AlbertPhan/stat-tracker/include/usb-cdc.c

/**
 * USB CDC Implementation
 * Based on the example from
 * https://github.com/Blinkinlabs/ch554_sdcc/tree/master/examples/usb_device_cdc_i2c
 *
 * Andreas Butti, (c) 2019
 * License: GPL
 */

#include "inc.h"
#include "usb-cdc.h"
#include "hardware.h"
//#include "logic.h"
#include "usb-descriptor.h"
//#include "parser.h"
//#include "eeprom.h"


/**
 * Last setup request
 */
__xdata uint8_t g_SetupReq;

/**
 * USB Configuration, can be read and written by the host
 */
__xdata uint8_t g_UsbConfig;

/**
 * Pointer to the current configuration data,
 * this pointer is incremented on transmission,
 * if a block is sent, while g_SetupLen is decremented
 */
const uint8_t* g_pDescr;

/**
 * Setup length, is decremented if a block is sent, see g_pDescr
 */
__xdata uint16_t g_SetupLen;

// Buffer for dynamic generated setup responses
__xdata uint8_t g_SetupRamBuffer[34];

/**
 * Use the received data as Setup request
 */
#define UsbSetupBuf	((PUSB_SETUP_REQ)Ep0Buffer)

// Configures DTE rate, stop-bits, parity, and number-of-character
#define SET_LINE_CODING 0X20

// This request allows the host to find out the currently configured line coding.
#define GET_LINE_CODING 0X21

// This request generates RS-232/V.24 style control signals
#define SET_CONTROL_LINE_STATE 0X22

/**
 * Baud rate, not needed for Virtual USB without hardware Serial
 * But may this is needed for another project, therefore this
 * will not be removed
 */
uint32_t g_Baud = 0;

// CDC parameter
// The initial baud rate is 57600, 1 stop bit, no parity, 8 data bits.
__xdata uint8_t g_LineCoding[7] = { 0x00, 0xe1, 0x00, 0x00, 0x00, 0x00, 0x08 };

// Serial receive buffer size
#define UART_REV_LEN 64

// Serial receive buffer
__idata uint8_t g_Receive_Uart_Buf[UART_REV_LEN];

// The circular buffer write pointer, the bus reset needs to be initialized to 0
volatile __idata uint8_t g_Uart_Input_Point = 0;

// The circular buffer fetches the pointer, and the bus reset needs to be initialized to 0.
volatile __idata uint8_t g_Uart_Output_Point = 0;

// Current buffer remaining bytes to be fetched
volatile __idata uint8_t g_UartByteCount = 0;

// Data received on behalf of the USB endpoint
volatile __idata uint8_t g_USBByteCount = 0;

// Data pointer
volatile __idata uint8_t g_USBBufOutPoint = 0;

// Upload endpoint is busy flag
volatile __idata uint8_t g_UpPoint2_Busy = 0;

/**
 * Handle USB Reset
 */
inline void usbResetInterrupt() {
	UEP0_CTRL = UEP_R_RES_ACK | UEP_T_RES_NAK;
	UEP1_CTRL = bUEP_AUTO_TOG | UEP_T_RES_NAK;
	UEP2_CTRL = bUEP_AUTO_TOG | UEP_T_RES_NAK | UEP_R_RES_ACK;
	USB_DEV_AD = 0x00;
	UIF_SUSPEND = 0;
	UIF_TRANSFER = 0;

	// Clear interrupt flag
	UIF_BUS_RST = 0;

	// Circular buffer input pointer
	g_Uart_Input_Point = 0;

	// Circular buffer read pointer
	g_Uart_Output_Point = 0;

	// Current buffer remaining bytes to be fetched
	g_UartByteCount = 0;

	// Length received by the USB endpoint
	g_USBByteCount = 0;

	// Clear configuration value
	g_UsbConfig = 0;
	g_UpPoint2_Busy = 0;
}

/**
 * Handle USB Suspend
 */
inline void usbWakeupSuspendInterrupt() {
	if (USB_MIS_ST & bUMS_SUSPEND) {
		while (XBUS_AUX & bUART0_TX) {
			; // Waiting for transmission to complete
		}

		// Before turning of the CPU turn OFF the LEDs
		//turnOffLeds();

		SAFE_MOD = 0x55;
		SAFE_MOD = 0xAA;

		// USB or RXD0/1 can be woken up when there is a signal
		WAKE_CTRL = bWAK_BY_USB | bWAK_RXD0_LO | bWAK_RXD1_LO;

		// Sleep
		PCON |= PD;

		SAFE_MOD = 0x55;
		SAFE_MOD = 0xAA;
		WAKE_CTRL = 0x00;
	}
}


/**
 * Transmit a Setup Block, increment pointer,
 * decrement remaining block length.
 * Calculate Length
 *
 * @param len Length
 * @return Length
 */
uint8_t transmitSetupBlock(uint8_t len) {
	// This transmission length
	len = g_SetupLen >= DEFAULT_ENDP0_SIZE ? DEFAULT_ENDP0_SIZE : g_SetupLen;

	// Load upload data, increment pointer, so the data is transmitted in Blocks
	memcpy(Ep0Buffer, g_pDescr, len);
	g_SetupLen -= len;
	g_pDescr += len;

	return len;
}


/**
 * Check if there is a custom PID / VID Configured, and overwrite the basic one
 * This is used to force e.g. Windows 7 to use a specific driver
 
void prepareUsbIds() {
	uint8_t a = 0;

	if (ReadDataFlash(4, 1, &a) != 1) {
		return;
	}

	// Use this char at pos 5 on EEPROM to mark the PID / VID should be loaded
	if (a != '>') {
		return;
	}

	if (ReadDataFlash(0, 1, &a) != 1) {
		return;
	}
	g_SetupRamBuffer[9] = a;

	if (ReadDataFlash(1, 1, &a) != 1) {
		return;
	}
	g_SetupRamBuffer[8] = a;

	if (ReadDataFlash(2, 1, &a) != 1) {
		return;
	}
	g_SetupRamBuffer[11] = a;

	if (ReadDataFlash(3, 1, &a) != 1) {
		return;
	}
	g_SetupRamBuffer[10] = a;
}
*/

/**
 * Read custom serial from EEPROM
 *
 * @return Len, 0x00 if nothing was read
 
inline uint8_t readNameFromEeprom() {
	uint8_t i;

	if (ReadDataFlash(24, sizeof(g_SetupRamBuffer) - 2, g_SetupRamBuffer + 2) != 1) {

		for (i = 2; i < sizeof(g_SetupRamBuffer) - 1; i += 2) {

			if (g_SetupRamBuffer[i] == 255 || (g_SetupRamBuffer[i] == 0 && g_SetupRamBuffer[i + 1] == 0)) {
				if (i > 2) {
					return i;
				} else {
					break;
				}
			}
		}
	}

	return 0x00;
}
*/

/**
 * Process USB Standard setup request
 *
 * @return Length
 */
inline uint8_t processUsbDescriptionRequest() {
	uint8_t len = 0;

	switch (UsbSetupBuf->wValueH) {
	// Device descriptor
	case 1:
		// Send the device descriptor to the buffer to be sent
		len = sizeof(g_DescriptorDevice);
		memcpy(g_SetupRamBuffer, g_DescriptorDevice, len);

		// Update USB IDs 
		//prepareUsbIds();
		// commented out to disable EEPROM ID functionality

		g_pDescr = g_SetupRamBuffer;
		break;

	// Configuration descriptor
	case 2:
		// Send the device descriptor to the buffer to be sent
		g_pDescr = g_DescriptorConfiguration;
		len = sizeof(g_DescriptorConfiguration);
		break;

	case 3:
		if (UsbSetupBuf->wValueL == 0) {
			g_pDescr = g_DescriptorLanguage;
			len = sizeof(g_DescriptorLanguage);

		} else if (UsbSetupBuf->wValueL == 1) {
			g_pDescr = g_DescriptorManufacturer;
			len = sizeof(g_DescriptorManufacturer);

		} else if (UsbSetupBuf->wValueL == 2) {
			/*
			len = readNameFromEeprom();
			if (len == 0x00) {
				g_pDescr = g_DescriptorProduct;
				len = sizeof(g_DescriptorProduct);
			} else {
				g_pDescr = g_SetupRamBuffer;
				g_SetupRamBuffer[0] = len;
				g_SetupRamBuffer[1] = 3;
			}
			*/
			g_pDescr = g_DescriptorProduct;
			len = sizeof(g_DescriptorProduct);			
		} else {
			g_pDescr = g_DescriptorSerial;
			len = sizeof(g_DescriptorSerial);
		}
		break;

	default:
		// Unsupported command or error
		len = 0xff;
		break;
	}

	if (g_SetupLen > len) {
		// Limit total length
		g_SetupLen = len;
	}

	return transmitSetupBlock(len);
}

/**
 * Process USB Standard setup clear request
 *
 * @return Length
 */
inline uint8_t processStandardSetupClearRequest() {
	uint8_t len = 0;

	// Clear device
	if ((UsbSetupBuf->bRequestType & 0x1F) == USB_REQ_RECIP_DEVICE) {
		if ((((uint16_t) UsbSetupBuf->wValueH << 8) | UsbSetupBuf->wValueL) == 0x01) {
			if (g_DescriptorConfiguration[7] & 0x20) {
				// wake
			} else {
				// operation failed
				len = 0xff;
			}
		} else {
			// operation failed
			len = 0xff;
		}

	} else if ((UsbSetupBuf->bRequestType & USB_REQ_RECIP_MASK) == USB_REQ_RECIP_ENDP) {
		switch (UsbSetupBuf->wIndexL) {
		case 0x83:
			UEP3_CTRL = UEP3_CTRL & ~(bUEP_T_TOG | MASK_UEP_T_RES) | UEP_T_RES_NAK;
			break;

		case 0x03:
			UEP3_CTRL = UEP3_CTRL & ~(bUEP_R_TOG | MASK_UEP_R_RES) | UEP_R_RES_ACK;
			break;

		case 0x82:
			UEP2_CTRL = UEP2_CTRL & ~(bUEP_T_TOG | MASK_UEP_T_RES) | UEP_T_RES_NAK;
			break;

		case 0x02:
			UEP2_CTRL = UEP2_CTRL & ~(bUEP_R_TOG | MASK_UEP_R_RES) | UEP_R_RES_ACK;
			break;

		case 0x81:
			UEP1_CTRL = UEP1_CTRL & ~(bUEP_T_TOG | MASK_UEP_T_RES) | UEP_T_RES_NAK;
			break;

		case 0x01:
			UEP1_CTRL = UEP1_CTRL & ~(bUEP_R_TOG | MASK_UEP_R_RES) | UEP_R_RES_ACK;
			break;

		default:
			// Unsupported endpoint
			len = 0xff;
			break;
		}

	} else {
		// No endpoints are not supported
		len = 0xff;
	}
	return len;
}

/**
 * Process USB Standard setup set feature request
 *
 * @return Length
 */
inline uint8_t processStandardSetupSetFeatureRequest() {
	// defaults to operation failed
	uint8_t len = 0xff;

	// Setting up the device
	if ((UsbSetupBuf->bRequestType & 0x1F) == USB_REQ_RECIP_DEVICE) {
		if ((((uint16_t) UsbSetupBuf->wValueH << 8) | UsbSetupBuf->wValueL) == 0x01) {
			if (g_DescriptorConfiguration[7] & 0x20) {
				// Sleep
				while (XBUS_AUX & bUART0_TX) {
					;	// Waiting for transmission to complete
				}

				SAFE_MOD = 0x55;
				SAFE_MOD = 0xAA;

				// USB or RXD0 / 1 can be woken up when there is a signal
				WAKE_CTRL = bWAK_BY_USB | bWAK_RXD0_LO | bWAK_RXD1_LO;

				// Sleep
				PCON |= PD;

				SAFE_MOD = 0x55;
				SAFE_MOD = 0xAA;
				WAKE_CTRL = 0x00;

				// result success
				len = 0;
			}
		}

		// Set endpoint
	} else if ((UsbSetupBuf->bRequestType & 0x1F) == USB_REQ_RECIP_ENDP) {
		if ((((uint16_t) UsbSetupBuf->wValueH << 8) | UsbSetupBuf->wValueL) == 0x00) {
			// result success
			len = 0;

			switch (((uint16_t) UsbSetupBuf->wIndexH << 8) | UsbSetupBuf->wIndexL) {
			case 0x83:
				// Set endpoint 3 IN STALL
				UEP3_CTRL = UEP3_CTRL & (~bUEP_T_TOG) | UEP_T_RES_STALL;
				break;

			case 0x03:
				// Set Endpoint 3 OUT Stall
				UEP3_CTRL = UEP3_CTRL & (~bUEP_R_TOG) | UEP_R_RES_STALL;
				break;

			case 0x82:
				// Set endpoint 2 IN STALL
				UEP2_CTRL = UEP2_CTRL & (~bUEP_T_TOG) | UEP_T_RES_STALL;
				break;

			case 0x02:
				// Set Endpoint 2 OUT Stall
				UEP2_CTRL = UEP2_CTRL & (~bUEP_R_TOG) | UEP_R_RES_STALL;
				break;

			case 0x81:
				// Set endpoint 1 IN STALL
				UEP1_CTRL = UEP1_CTRL & (~bUEP_T_TOG) | UEP_T_RES_STALL;
				break;

			case 0x01:
				// Set endpoint 1 OUT Stall
				UEP1_CTRL = UEP1_CTRL & (~bUEP_R_TOG) | UEP_R_RES_STALL;
				break;

			default:
				// operation failed
				len = 0xff;
				break;
			}
		}
	}

	return len;
}

/**
 * Process USB Standard setup request
 *
 * @return Length
 */
inline uint8_t processStandardSetupRequest() {
	uint8_t len = 0;

	// Request code
	switch (g_SetupReq) {
	case USB_GET_DESCRIPTOR:
		len = processUsbDescriptionRequest();
		break;

	case USB_SET_ADDRESS:
		// Staging USB device address
		g_SetupLen = UsbSetupBuf->wValueL;
		break;

	case USB_GET_CONFIGURATION:
		Ep0Buffer[0] = g_UsbConfig;
		if (g_SetupLen >= 1) {
			len = 1;
		}
		break;

	case USB_SET_CONFIGURATION:
		g_UsbConfig = UsbSetupBuf->wValueL;
		break;

	case USB_GET_INTERFACE:
		break;

		//Clear Feature
	case USB_CLEAR_FEATURE:
		len = processStandardSetupClearRequest();
		break;

	// Set Feature
	case USB_SET_FEATURE:
		len = processStandardSetupSetFeatureRequest();
		break;

	case USB_GET_STATUS:
		Ep0Buffer[0] = 0x00;
		Ep0Buffer[1] = 0x00;
		if (g_SetupLen >= 2) {
			len = 2;
		} else {
			len = g_SetupLen;
		}
		break;

	// operation failed
	default:
		len = 0xff;
		break;
	}

	return len;
}

/**
 * Process USB Non-Standard setup request
 *
 * @return Length
 */
inline uint8_t processNonStandardSetupRequest() {
	uint8_t len = 0;

	switch (g_SetupReq) {
	// This request allows the host to find out the currently configured line coding.
	case GET_LINE_CODING:
		g_pDescr = g_LineCoding;
		len = sizeof(g_LineCoding);

		len = transmitSetupBlock(len);
		break;

	// This request generates RS-232/V.24 style control signals
	case SET_CONTROL_LINE_STATE:
		break;

	case SET_LINE_CODING:
		break;

	default:
		// Command not supported
		len = 0xff;
		break;
	}

	return len;
}

/**
 * Process the Setup request, and return the length of the packet
 *
 * @return Length
 */
uint8_t processSetupRequest() {
	// The default is success and upload 0 length
	uint8_t len = 0;

	g_SetupLen = ((uint16_t) UsbSetupBuf->wLengthH << 8) | (UsbSetupBuf->wLengthL);
	g_SetupReq = UsbSetupBuf->bRequest;

	// Non-standard request
	if ((UsbSetupBuf->bRequestType & USB_REQ_TYP_MASK) != USB_REQ_TYP_STANDARD) {
		len = processNonStandardSetupRequest();
	} else { // Standard request
		len = processStandardSetupRequest();
	}

	return len;
}

/**
 * USB Setup Handler
 */
inline void usbSetupInterrupt() {
	uint8_t len;
	if (USB_RX_LEN == sizeof(USB_SETUP_REQ)) {
		len = processSetupRequest();
	} else {
		// Wrong packet length
		len = 0xff;
	}

	if (len == 0xff) {
		g_SetupReq = 0xff;

		// STALL
		UEP0_CTRL = bUEP_R_TOG | bUEP_T_TOG | UEP_R_RES_STALL | UEP_T_RES_STALL;

	} else if (len <= DEFAULT_ENDP0_SIZE) {
		// Upload data or status stage returns 0 length package

		UEP0_T_LEN = len;
		// The default packet is DATA1, which returns a response ACK.
		UEP0_CTRL = bUEP_R_TOG | bUEP_T_TOG | UEP_R_RES_ACK | UEP_T_RES_ACK;

	} else {
		// Although it has not yet reached the status stage,
		// it uploads 0 length data packets in advance to prevent
		// the host from entering the status stage in advance.
		UEP0_T_LEN = 0;

		// The default packet is DATA1, which returns a response ACK.
		UEP0_CTRL = bUEP_R_TOG | bUEP_T_TOG | UEP_R_RES_ACK | UEP_T_RES_ACK;
	}
}

/**
 * Handle USB Data transfer
 */
inline void usbTransferInterrupt() {
	uint16_t len;

	switch (USB_INT_ST & (MASK_UIS_TOKEN | MASK_UIS_ENDP)) {
	// Endpoint 1# Endpoint interrupt upload
	case UIS_TOKEN_IN | 1:
		// Pre-use send length must be cleared
		UEP1_T_LEN = 0;

		// Default response NAK
		UEP1_CTRL = UEP1_CTRL & ~ MASK_UEP_T_RES | UEP_T_RES_NAK;
		break;

	// Endpoint 2# Endpoint bulk upload
	case UIS_TOKEN_IN | 2:
		// Pre-use send length must be cleared
		UEP2_T_LEN = 0;

		// Default response NAK
		UEP2_CTRL = UEP2_CTRL & ~ MASK_UEP_T_RES | UEP_T_RES_NAK;

		// Clear busy flag
		g_UpPoint2_Busy = 0;
		break;

	// Endpoint 3# Endpoint Batch Down
	case UIS_TOKEN_OUT | 2:
		// Out of sync packets will be dropped
		if (U_TOG_OK) {
			g_USBByteCount = USB_RX_LEN;

			// Take data pointer reset
			g_USBBufOutPoint = 0;

			// Receive a packet of data on the NAK,
			// the main function is processed,
			// and the main function modifies the response mode.
			UEP2_CTRL = UEP2_CTRL & ~ MASK_UEP_R_RES | UEP_R_RES_NAK;
		}
		break;

	// SETUP transaction
	case UIS_TOKEN_SETUP | 0:
		usbSetupInterrupt();
		break;

	// endpoint0 IN
	case UIS_TOKEN_IN | 0:
		switch (g_SetupReq) {
		case USB_GET_DESCRIPTOR:
			len = transmitSetupBlock(len);
			UEP0_T_LEN = len;

			// Sync flag bit flip
			UEP0_CTRL ^= bUEP_T_TOG;
			break;

		case USB_SET_ADDRESS:
			USB_DEV_AD = USB_DEV_AD & bUDA_GP_BIT | g_SetupLen;
			UEP0_CTRL = UEP_R_RES_ACK | UEP_T_RES_NAK;
			break;

		default:
			// The status phase completes the interrupt or is forced to upload 0 length packet end control transmission
			UEP0_T_LEN = 0;
			UEP0_CTRL = UEP_R_RES_ACK | UEP_T_RES_NAK;
			break;
		}
		break;

	// endpoint0 OUT
	case UIS_TOKEN_OUT | 0:
		//Set the serial port properties
		if (g_SetupReq == SET_LINE_CODING) {
			if (U_TOG_OK) {
				memcpy(g_LineCoding, UsbSetupBuf, USB_RX_LEN);
				*((uint8_t *) &g_Baud) = g_LineCoding[0];
				*((uint8_t *) &g_Baud + 1) = g_LineCoding[1];
				*((uint8_t *) &g_Baud + 2) = g_LineCoding[2];
				*((uint8_t *) &g_Baud + 3) = g_LineCoding[3];

				if (g_Baud > 999999) {
					g_Baud = 57600;
				}

				UEP0_T_LEN = 0;

				// Ready to upload 0 packages
				UEP0_CTRL |= UEP_R_RES_ACK | UEP_T_RES_ACK;
			}
		} else {
			UEP0_T_LEN = 0;
			// Just ACK is fine.
			UEP0_CTRL |= UEP_R_RES_ACK | UEP_T_RES_ACK;
		}
		break;

	default:
		break;
	}
}

/**
 * USB Interrupt Handler, this is called by main.c,
 * the main Hardware interrupt handler
 */
void usbInterrupt() {
	// USB transfer completion flag
	if (UIF_TRANSFER) {
		usbTransferInterrupt();

		// Write 0 to clear interrupt
		UIF_TRANSFER = 0;
	}

	// Device Mode USB Bus Reset Interrupt
	if (UIF_BUS_RST) {
		usbResetInterrupt();
	}

	// USB bus suspend / wake up
	if (UIF_SUSPEND) {
		UIF_SUSPEND = 0;

		usbWakeupSuspendInterrupt();
	} else {
		// Unexpected interruption, impossible situation

		// Clear interrupt flag
		USB_INT_FG = 0xFF;
	}
}

/**
 * Send one byte over USB CDC Serial port
 */
void UsbCdc_putc(uint8_t tdata) {
	g_Receive_Uart_Buf[g_Uart_Input_Point++] = tdata;

	// Current buffer remaining bytes to be fetched
	g_UartByteCount++;
	if (g_Uart_Input_Point >= UART_REV_LEN) {
		g_Uart_Input_Point = 0;
	}
}

/**
 * Send uint8_t over CDC Serial port
 */
void UsbCdc_puti(uint8_t value) {
	__xdata uint8_t i = 3;
	__xdata char data[4];
	data[3] = 0;

	if (value == 0) {
		UsbCdc_putc('0');
		return;
	}

	while (value > 0) {
		i--;
		data[i] = (value % 10) + '0';
		value /= 10;
	}

	UsbCdc_puts(data + i);
}

/**
 * Send uint32_t over CDC Serial port
 */
void UsbCdc_puti32(uint32_t value) {
	__xdata uint8_t i = 10;	// 10 digits to represent 32 bit
	__xdata char data[11];
	data[10] = 0;

	if (value == 0) {
		UsbCdc_putc('0');
		return;
	}

	while (value > 0) {
		i--;
		data[i] = (value % 10) + '0';
		value /= 10;
	}

	UsbCdc_puts(data + i);
}

/**
 * Send 0 terminated string over USB CDC Serial port
 */
void UsbCdc_puts(char* str) {
	while (*str) {
		UsbCdc_putc(*(str++));
	}
}

/**
 * Send usb data from buffer
 */
void UsbCdc_processOutput() {
	static uint8_t uartTimeout = 0;

	if (g_UsbConfig) {
		if (g_UartByteCount) {
			uartTimeout++;
		}

		// The endpoint is not busy (the first packet of data after idle, only used to trigger the upload)
		if (!g_UpPoint2_Busy) {
			uint8_t length = g_UartByteCount;
			if (length > 0) {
				if (length > 39 || uartTimeout > 100) {
					uartTimeout = 0;
					if (g_Uart_Output_Point + length > UART_REV_LEN) {
						length = UART_REV_LEN - g_Uart_Output_Point;
					}

					g_UartByteCount -= length;
					// Write upload endpoint
					memcpy(Ep2Buffer + MAX_PACKET_SIZE, &g_Receive_Uart_Buf[g_Uart_Output_Point], length);
					g_Uart_Output_Point += length;
					if (g_Uart_Output_Point >= UART_REV_LEN) {
						g_Uart_Output_Point = 0;
					}

					// Pre-use send length must be cleared
					UEP2_T_LEN = length;

					// Answer ACK
					UEP2_CTRL = UEP2_CTRL & ~ MASK_UEP_T_RES | UEP_T_RES_ACK;
					g_UpPoint2_Busy = 1;
				}
			}
		}
	}
}

/**
 * Receive data from USB and process it, process only one byte at once
 */
void UsbCdc_processInput() {
	if (g_USBByteCount) {
		//parseCmd(Ep2Buffer[g_USBBufOutPoint++]);

		g_USBByteCount--;

		if (g_USBByteCount == 0) {
			UEP2_CTRL = UEP2_CTRL & ~ MASK_UEP_R_RES | UEP_R_RES_ACK;
		}
	}
}
