AlbertPhan/stat-tracker/include/usb-descriptor.h

/**
 * USB Descriptors
 *
 * Andreas Butti, (c) 2019
 * License: GPL
 */

#pragma once

#include "inc.h"

// Device descriptor
__code uint8_t g_DescriptorDevice[] = {
	0x12, 0x01, 0x10, 0x01,
	0x02, 0x00, 0x00, DEFAULT_ENDP0_SIZE,

	// Shared vendor / product id from V-USB / obdev.at
	// Vendor
	0xC0, 0x16,

	// Product
	0xdd, 0x27,

	0x00, 0x01, 0x01, 0x02,
	0x03, 0x01
};

__code uint8_t g_DescriptorConfiguration[] = {
	// ------------------------------------------------------------------------
	// Configuration descriptor (two interfaces)
	// ------------------------------------------------------------------------
	0x09, 0x02, 0x43, 0x00, 0x02, 0x01, 0x00, 0xa0, 0x32,

	// ------------------------------------------------------------------------
	// The following is the interface 0 (CDC interface) descriptor
	// ------------------------------------------------------------------------

	// CDC interface descriptor (one endpoint)
	0x09, 0x04, 0x00, 0x00, 0x01, 0x02, 0x02, 0x01, 0x00,

	// ------------------------------------------------------------------------
	// The following is the function descriptor
	// ------------------------------------------------------------------------

	// Function descriptor (header)
	0x05, 0x24, 0x00, 0x10, 0x01,

	// Management descriptor (no data class interface) 03 01
	0x05, 0x24, 0x01, 0x00, 0x00,

	// Support Set_Line_Coding, Set_Control_Line_State, Get_Line_Coding, Serial_State
	0x04, 0x24, 0x02, 0x02,

	// CDC interface numbered 0; data class interface number 1
	0x05, 0x24, 0x06, 0x00, 0x01,

	// Interrupt upload endpoint descriptor
	0x07, 0x05, 0x81, 0x03, 0x10, 0x00, 0x40,

	// ------------------------------------------------------------------------
	// The following is the interface 1 (data interface) descriptor
	// ------------------------------------------------------------------------

	// Data interface descriptor
	0x09, 0x04, 0x01, 0x00, 0x02, 0x0a, 0x00, 0x00, 0x00,

	// Endpoint descriptor
	0x07, 0x05, 0x02, 0x02, 0x40, 0x00, 0x00,

	// Endpoint descriptor
	0x07, 0x05, 0x82, 0x02, 0x40, 0x00, 0x00,
};

// ----------------------------------------------------------------------------
// String descriptor
// ----------------------------------------------------------------------------

// Language descriptor: English
unsigned char __code g_DescriptorLanguage[] = { 0x04, 0x03, 0x09, 0x04 };

// Serial number string descriptor
// Use this as identifier for Linux and Windows,
// the Name is the only Attribute displayed on Windows
unsigned char __code g_DescriptorSerial[] = {
	26, // Length of the whole array including this byte
	3,
	'C', 0, 'H', 0, '5', 0, '5', 0, '2', 0, ' ', 0,
	'S', 0, 'e', 0, 'r', 0, 'i', 0, 'a', 0, 'l', 0,
};

/*
unsigned char __code g_DescriptorSerial[] = {
	20, // Length of the whole array including this byte
	3,
	'S', 0, 't', 0, 'a', 0, 't', 0, 'e', 0, ' ', 0,
	'L', 0, 'E', 0, 'D', 0
};
*/



// Product string descriptor
unsigned char __code g_DescriptorProduct[] = {
	26, // Length of the whole array including this byte
	3,
	'C', 0, 'H', 0, '5', 0, '5', 0, '2', 0, ' ', 0,
	'S', 0, 'e', 0, 'r', 0, 'i', 0, 'a', 0, 'l', 0,
};

// Manufacturer string descriptor
unsigned char __code g_DescriptorManufacturer[] = {
	28, // Length of the whole array including this byte
	3,
	'A', 0, 'n', 0, 'd', 0, 'r', 0, 'e', 0, 'a', 0, 's', 0, ' ', 0,
	'B', 0, 'u', 0, 't', 0, 't', 0, 'i', 0
};
