AlbertPhan/stat-tracker/include/timer.h

/* timer.h
Utility to configure and set up the timer for ch552
Provides use of millis();
*/
#pragma once
#include <ch554.h>

#define LOOP_PERIOD_MS 10   // main loop period

#define enable_timer0_interrupt() (ET0 = 1)   // Enable timer 0 interrupt 
void timer0_init();
inline uint32_t millis();
void timer0_ISR() __interrupt (INT_NO_TMR0);
